StanleySun233/SHMTUBS/code/Book-Detection/data/origin/0.jpg

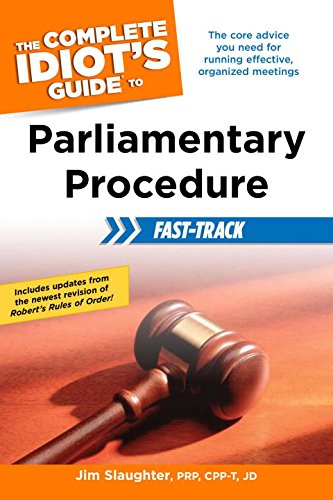
code/Book-Detection/data/origin/0.jpg
