StanleySun233/SHMTUBS/code/Book-Detection/data/origin/1.jpg

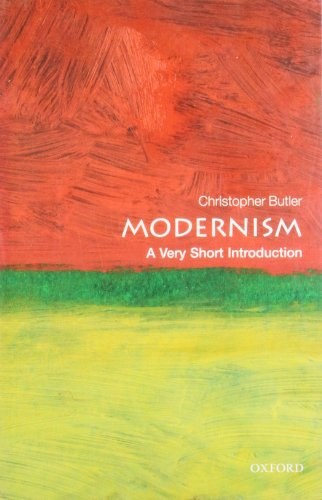
code/Book-Detection/data/origin/1.jpg
