StanleySun233/SHMTUBS/code/Book-Detection/data/origin/2.jpg

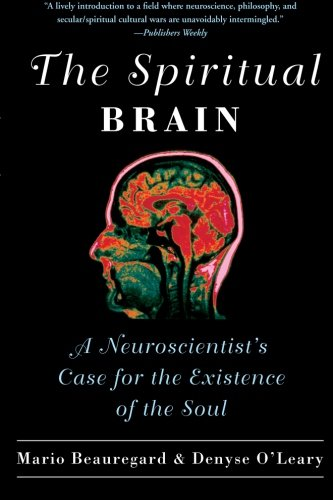
code/Book-Detection/data/origin/2.jpg
