StanleySun233/SHMTUBS/code/Book-Detection/data/origin/3.jpg

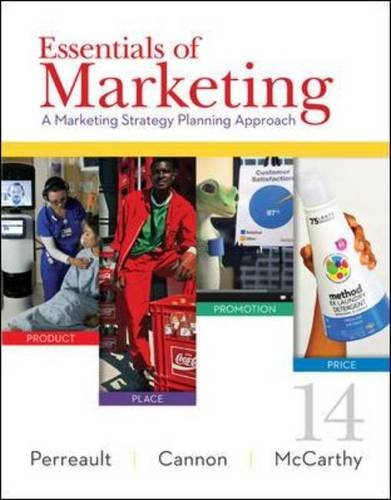
code/Book-Detection/data/origin/3.jpg
