StanleySun233/SHMTUBS/code/Book-Detection/data/origin/4.jpg

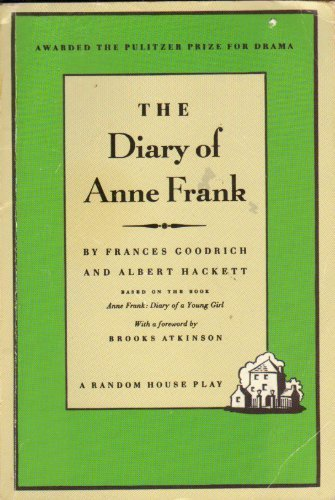
code/Book-Detection/data/origin/4.jpg
