StanleySun233/SHMTUBS/code/Book-Detection/data/origin/5.jpg

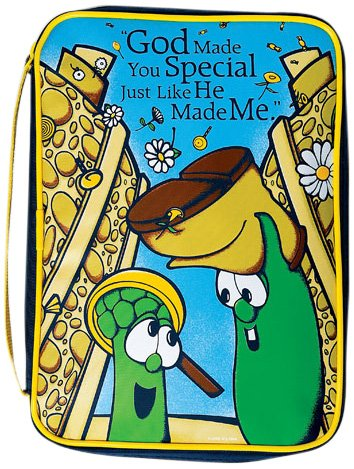
code/Book-Detection/data/origin/5.jpg
