StanleySun233/SHMTUBS/code/Book-Detection/data/origin/6.jpg

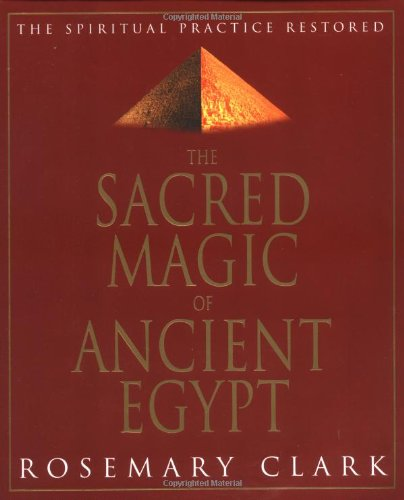
code/Book-Detection/data/origin/6.jpg
