StanleySun233/SHMTUBS/code/Book-Detection/data/origin/7.jpg

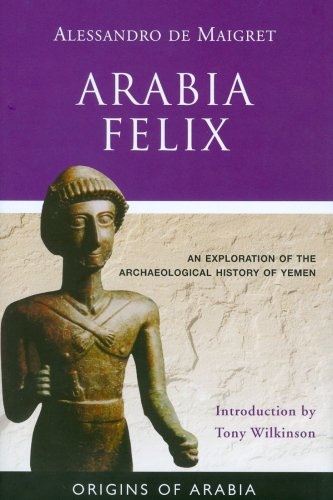
code/Book-Detection/data/origin/7.jpg
