StanleySun233/SHMTUBS/code/Book-Detection/data/origin/8.jpg

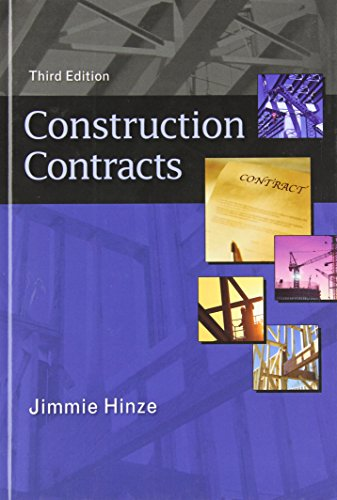
code/Book-Detection/data/origin/8.jpg
