StanleySun233/SHMTUBS/code/Book-Detection/data/origin/9.jpg

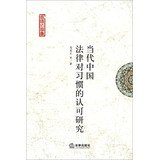
code/Book-Detection/data/origin/9.jpg
